Miceuz/i2c-moisture-sensor/pics/IMG_20160119_235137.jpg

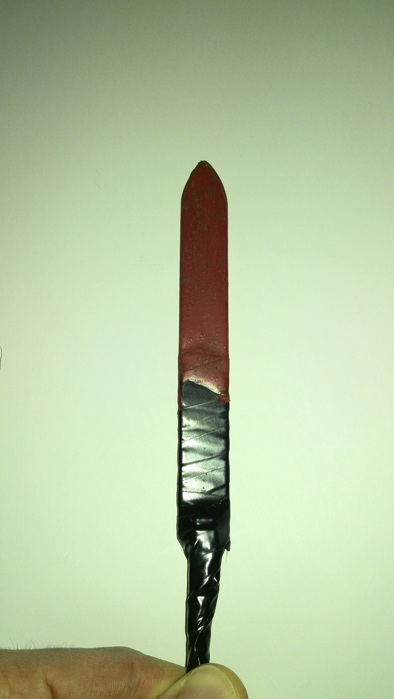
pics/IMG_20160119_235137.jpg
