Miceuz/i2c-moisture-sensor/src/programmer/firmware.h

#include <avr/pgmspace.h>

PROGMEM const unsigned int firmware[] = {
0xC01D, 0xC037, 0xC079, 0xC035, 0xC034, 0xC033, 0xC032, 0xC031, 
0xC0A8, 0xC02F, 0xC02E, 0xC02D, 0xC02C, 0xC042, 0xC02A, 0xC029, 
0xC028, 0xC027, 0xC026, 0xC025, 0xC024, 0xC023, 0xC022, 0xC021, 
0xC020, 0xC01F, 0xC01E, 0xC01D, 0xC01C, 0xC1F9, 0x2411, 0xBE1F, 
0xEFCF, 0xE0D1, 0xBFDE, 0xBFCD, 0xE011, 0xE0A0, 0xE0B1, 0xEDE8, 
0xE0F5, 0xC002, 0x9005, 0x920D, 0x35AA, 0x07B1, 0xF7D9, 0xE011, 
0xE5AA, 0xE0B1, 0xC001, 0x921D, 0x38A8, 0x07B1, 0xF7E1, 0xD0AA, 
0xC2B1, 0xCFC6, 0xB78B, 0x7E8F, 0xBF8B, 0xBC1E, 0x9891, 0x9878, 
0xE081, 0x9380, 0x0100, 0x9508, 0xB785, 0x7E87, 0x6088, 0xBF85, 
0xB785, 0x6280, 0xBF85, 0x9588, 0xB785, 0x7D8F, 0xBF85, 0x9508, 
0x921F, 0x920F, 0xB60F, 0x920F, 0x2411, 0x900F, 0xBE0F, 0x900F, 
0x901F, 0x9518, 0xB989, 0x9A2E, 0xDFE7, 0xB186, 0xB197, 0x9508, 
0xE081, 0x9380, 0x0163, 0xE083, 0xDFF5, 0xD15D, 0x9210, 0x0163, 
0x01CB, 0x9508, 0x93CF, 0x93DF, 0xE081, 0x9380, 0x0162, 0xE085, 
0xDFE9, 0x01EC, 0xE087, 0xDFE6, 0x9210, 0x0162, 0x5F9C, 0x1B8C, 
0x0B9D, 0x91DF, 0x91CF, 0x9508, 0x921F, 0x920F, 0xB60F, 0x920F, 
0x2411, 0x932F, 0x933F, 0x934F, 0x935F, 0x936F, 0x937F, 0x938F, 
0x939F, 0x93AF, 0x93BF, 0x93EF, 0x93FF, 0xB78B, 0x7E8F, 0xBF8B, 
0xBC1E, 0xB58C, 0xB59D, 0x9390, 0x0161, 0x9380, 0x0160, 0x9180, 
0x0160, 0x9190, 0x0161, 0x9390, 0x015F, 0x9380, 0x015E, 0xDF9A, 
0x91FF, 0x91EF, 0x91BF, 0x91AF, 0x919F, 0x918F, 0x917F, 0x916F, 
0x915F, 0x914F, 0x913F, 0x912F, 0x900F, 0xBE0F, 0x900F, 0x901F, 
0x9518, 0x921F, 0x920F, 0xB60F, 0x920F, 0x2411, 0x932F, 0x933F, 
0x934F, 0x935F, 0x936F, 0x937F, 0x938F, 0x939F, 0x93AF, 0x93BF, 
0x93EF, 0x93FF, 0xEF8F, 0xEF9F, 0x9390, 0x0161, 0x9380, 0x0160, 
0x9180, 0x0160, 0x9190, 0x0161, 0x9390, 0x015F, 0x9380, 0x015E, 
0xDF69, 0x91FF, 0x91EF, 0x91BF, 0x91AF, 0x919F, 0x918F, 0x917F, 
0x916F, 0x915F, 0x914F, 0x913F, 0x912F, 0x900F, 0xBE0F, 0x900F, 
0x901F, 0x9518, 0x93CF, 0x93DF, 0x921F, 0xB7CD, 0xB7DE, 0xBE14, 
0xED88, 0x9380, 0x0071, 0xB581, 0x7F87, 0xBD81, 0xE081, 0xE090, 
0xD1E3, 0x2F18, 0xD1A3, 0x1181, 0xC001, 0xE210, 0xE78E, 0x9380, 
0x0070, 0xE880, 0xB98A, 0xB98C, 0xEA88, 0x9380, 0x0060, 0xB38A, 
0x6083, 0xBB8A, 0x98D8, 0x98D9, 0xE885, 0xB985, 0x9A2B, 0xB818, 
0x9478, 0x9AD8, 0xDF55, 0x9390, 0x015B, 0x9380, 0x015A, 0xDF5A, 
0x9390, 0x015D, 0x9380, 0x015C, 0xEF2F, 0xEE81, 0xE094, 0x5021, 
0x4080, 0x4090, 0xF7E1, 0xC000, 0x0000, 0x98D8, 0x2F81, 0xD0F0, 
0xE013, 0xD148, 0x2388, 0xF3E9, 0xD14E, 0x1181, 0xC00C, 0x9180, 
0x015D, 0xD15C, 0x9180, 0x015C, 0xD159, 0xDF3C, 0x9390, 0x015D, 
0x9380, 0x015C, 0xCFEE, 0x3081, 0xF459, 0xD13D, 0x2F68, 0x8369, 
0xD15D, 0x8169, 0x2388, 0xF329, 0xE081, 0xE090, 0xD19D, 0xCFE1, 
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

};
#define FIRMWARE_WORD_COUNT  793
